rajdeepsaha2003/Prosthetic_Hand/Extra files/WhatsApp Image 2024-02-10 at 18.09.01_6530738f.jpg

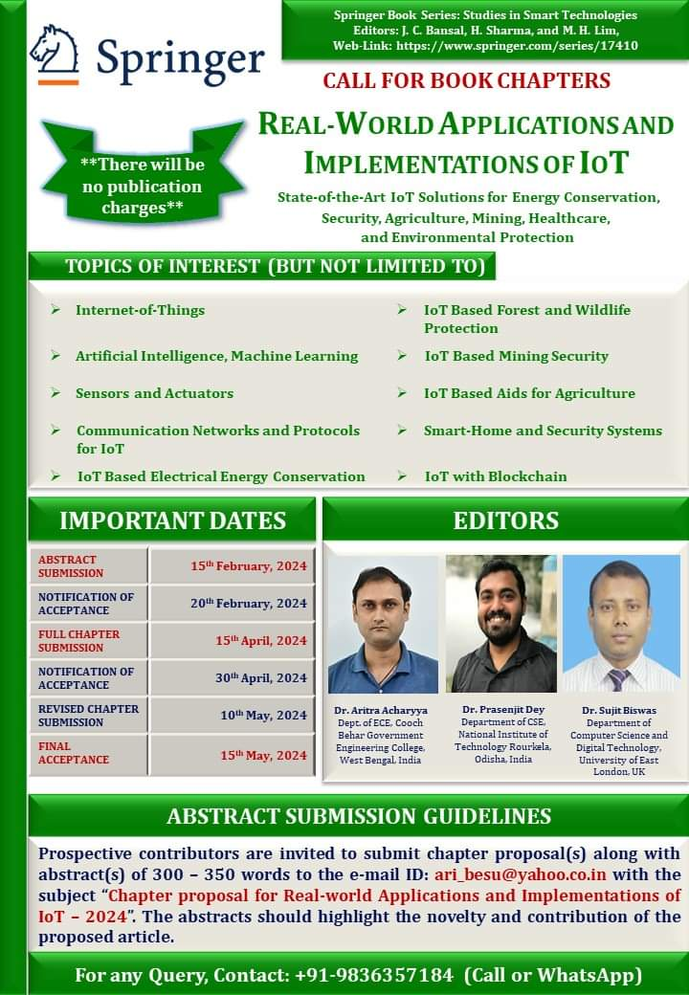
Extra files/WhatsApp Image 2024-02-10 at 18.09.01_6530738f.jpg
