rajdeepsaha2003/Prosthetic_Hand/Prosthetic_hand/3D Files Robo Hand/Screenshot 2024-03-03 145729.png

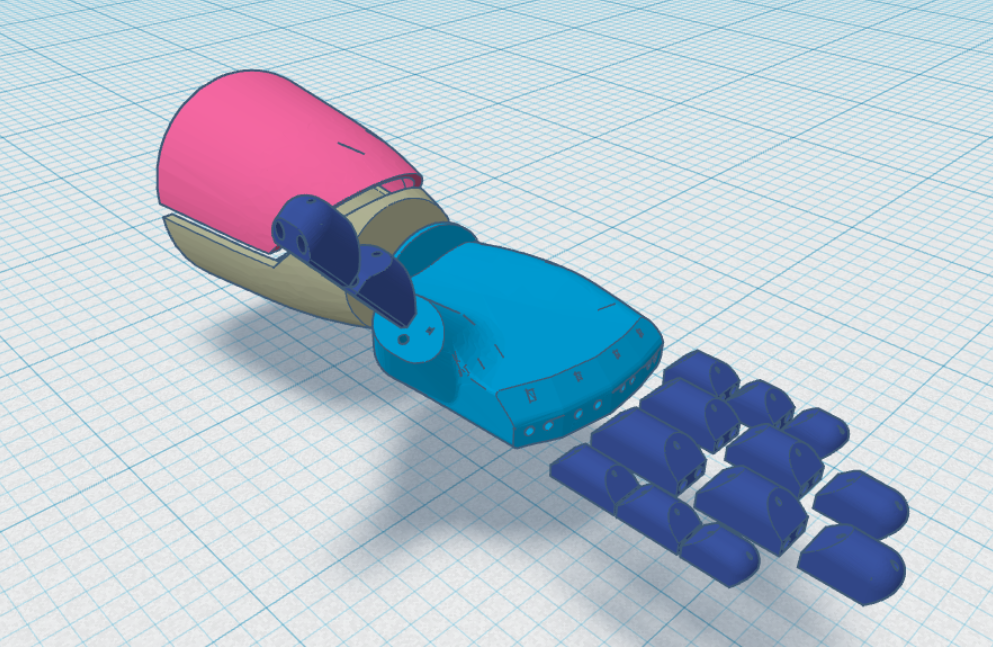
Prosthetic_hand/3D Files Robo Hand/Screenshot 2024-03-03 145729.png
